lambdakb/trackball-lt6c/output/img/lt6c-pcb-bottom.png

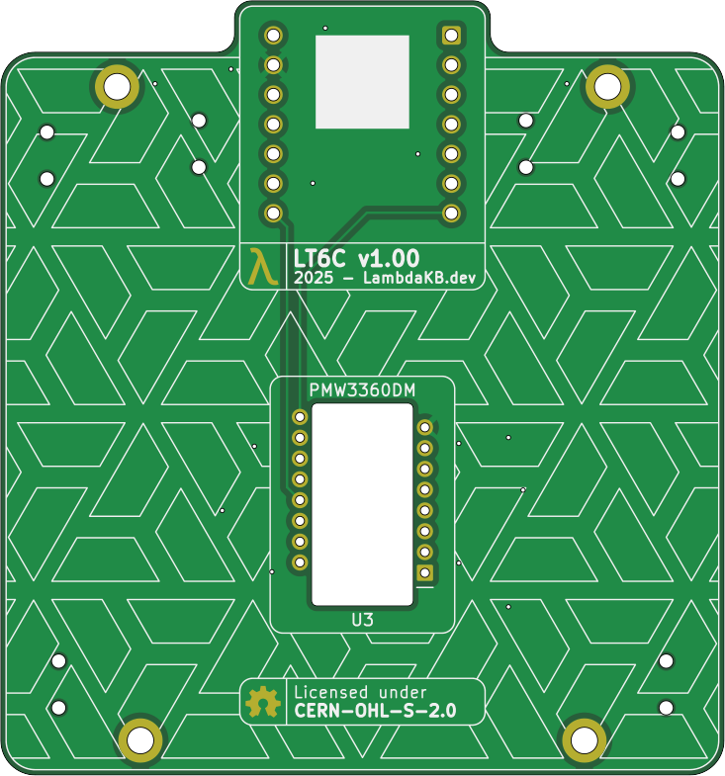
output/img/lt6c-pcb-bottom.png
