lambdakb/trackball-lt6c/output/img/lt6c-pcb-top.png

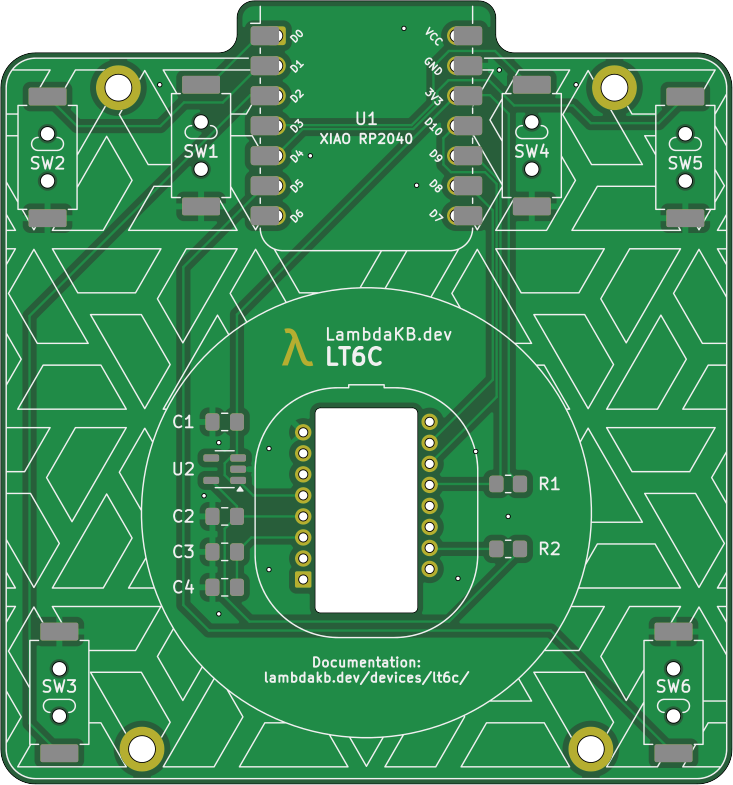
output/img/lt6c-pcb-top.png
